b1nc/Egg-On-Rice-Controller/Acrylic Layers/cutout_vs_no_cutout.png

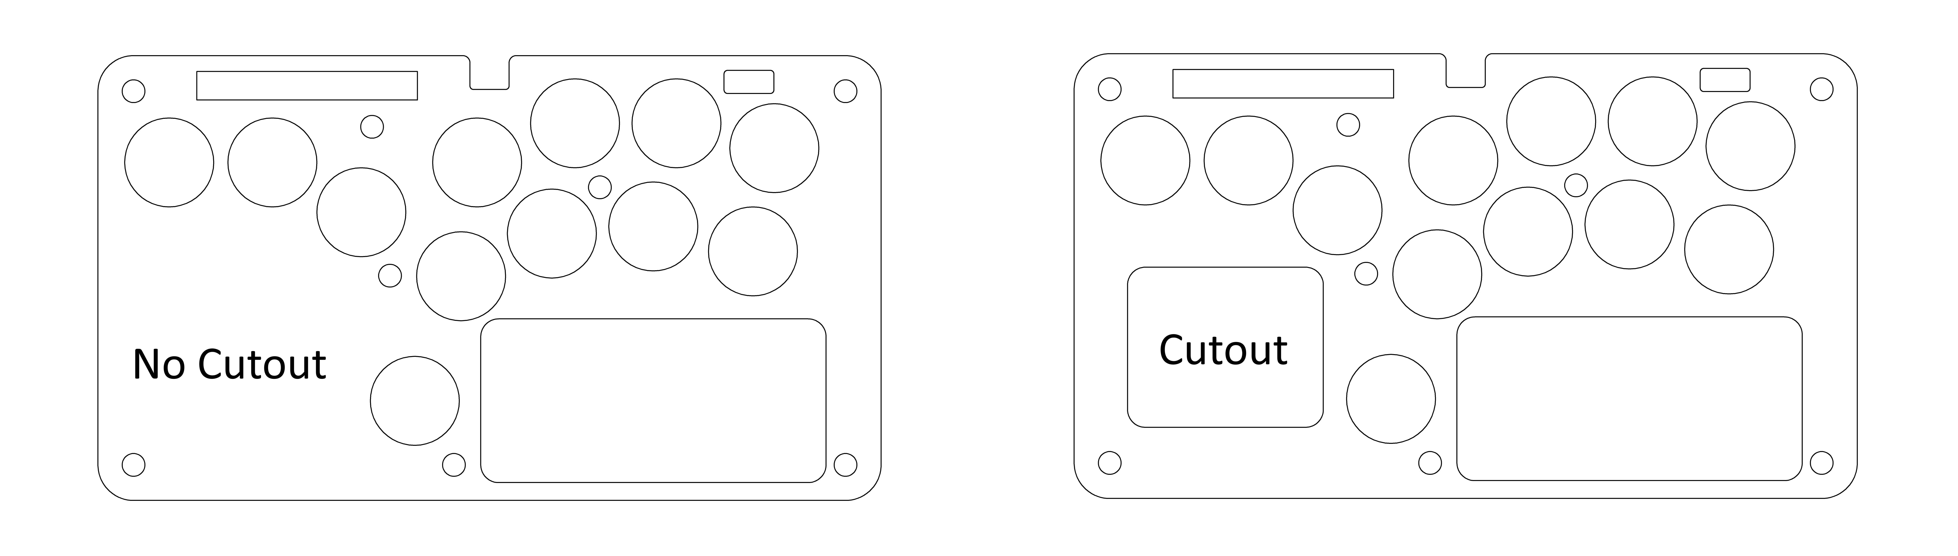
Acrylic Layers/cutout_vs_no_cutout.png
