b1nc/Egg-On-Rice-Controller/Acrylic Layers/layer_indication.PNG

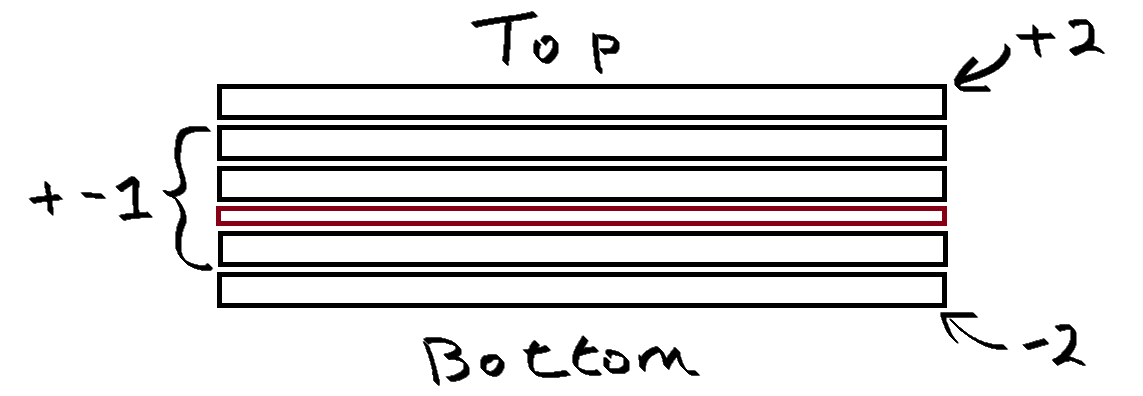
Acrylic Layers/layer_indication.PNG
